DonSlaughter/neopixel-binary-clock/sourcecode/src/main.h

#include <Arduino.h>
#include <Wire.h>

// Connect to Wi-Fi
/*
	create a file named secrets.h in the folder src.
	it should contain your wifi network (ssid) and your wifi password:
	const char *ssid = "";
	const char *pass = "";
*/

//Prototypes:
//Connect to WiFi Network described in secrets.h
void connect_to_wifi();
//Print the connection details on Serial Monitor
void print_connection();
//Update the RealtimeClock with NTP Server
//Gets epochTime from Timeserver and stores the value in the RTC
void RTC_Update();
//Print formatted Timestring on Serial Monitor
void printDateTime(time_t t, const char *tz);
//change color
void change_colors();
//Write the time to leds.
void WS2812B_Write_Time();
//Converts Time to led numbers
void WS2812B_Write_Number(uint8_t startIndex, uint8_t endIndex, uint8_t number, CHSV color);
//function to dimm the lights between two hours
void night_mode_on();
void night_mode_off();
//Debug Function to check if LED's work correctly
void test_all_leds();
